rganlath3/DarkPassenger/Visual_Documentation/Base_MCU_TopView.png

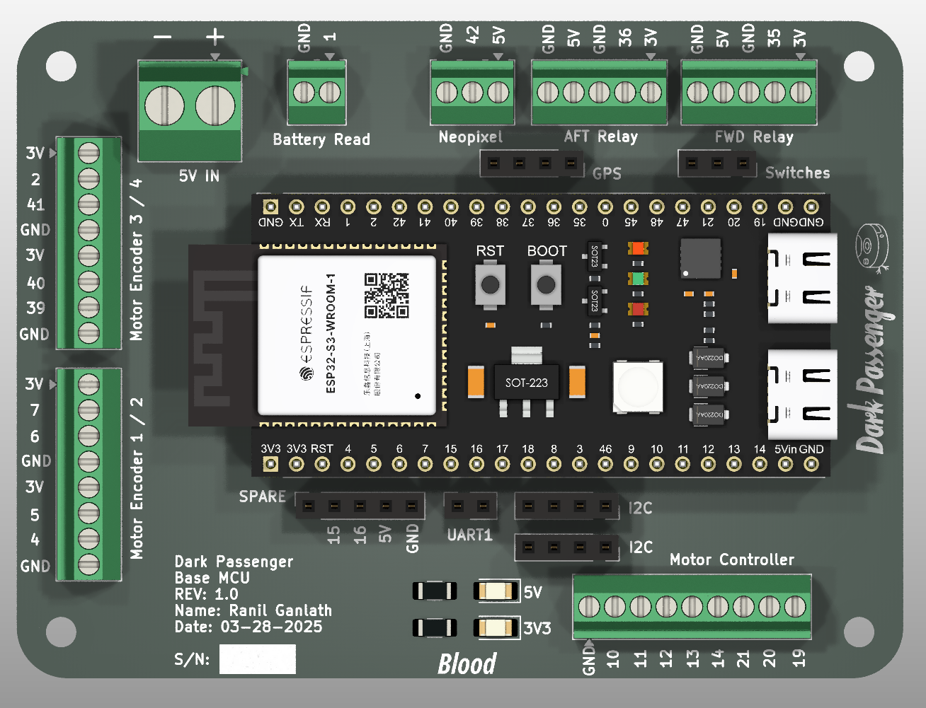
Visual_Documentation/Base_MCU_TopView.png
