rganlath3/DarkPassenger/Visual_Documentation/FrontView03192025.png

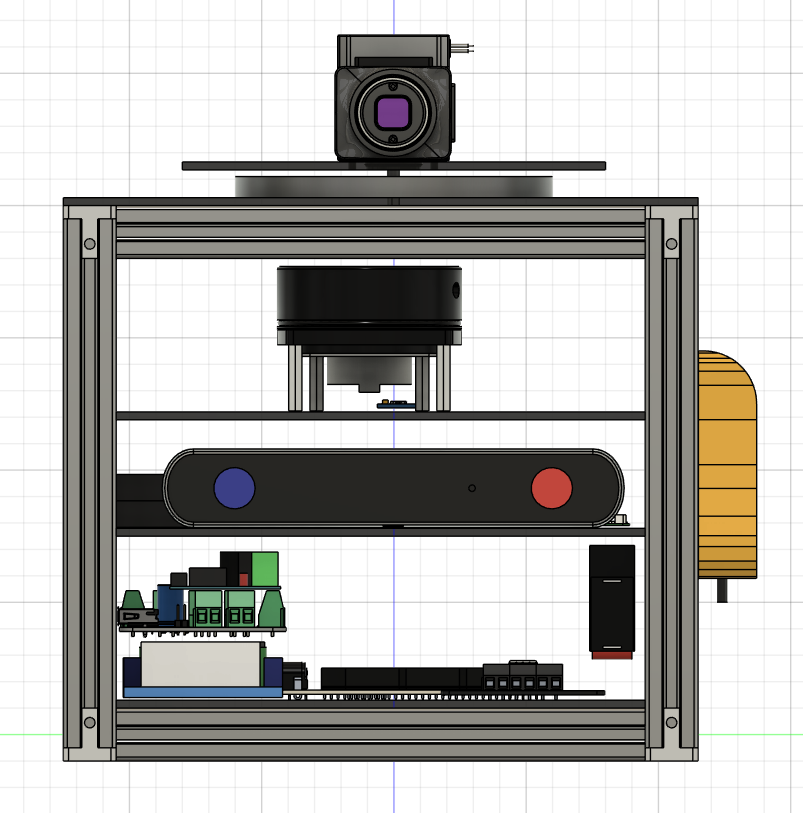
Visual_Documentation/FrontView03192025.png
