rganlath3/DarkPassenger/Visual_Documentation/PowerDistro_ISOUndersideView.png

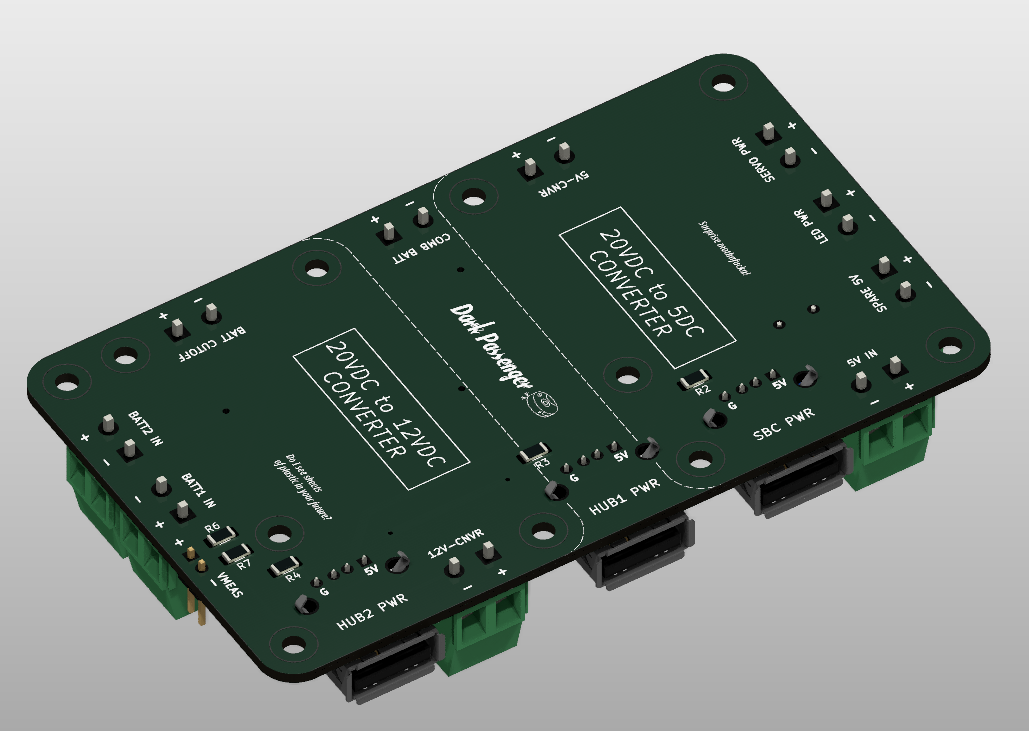
Visual_Documentation/PowerDistro_ISOUndersideView.png
