rganlath3/DarkPassenger/Visual_Documentation/SideView03192025.png

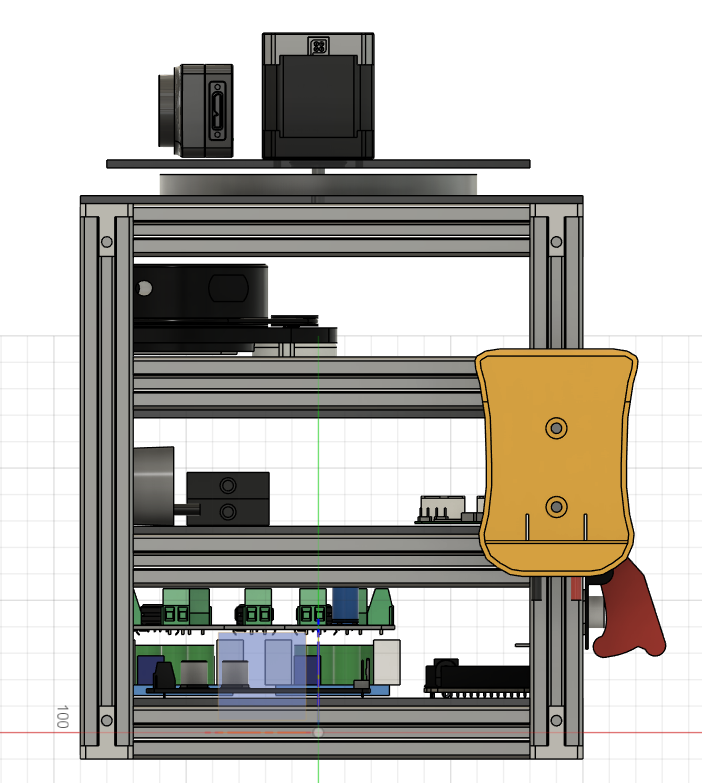
Visual_Documentation/SideView03192025.png
