rganlath3/DarkPassenger/Visual_Documentation/Turret_MCU_ISOUndersideView.png

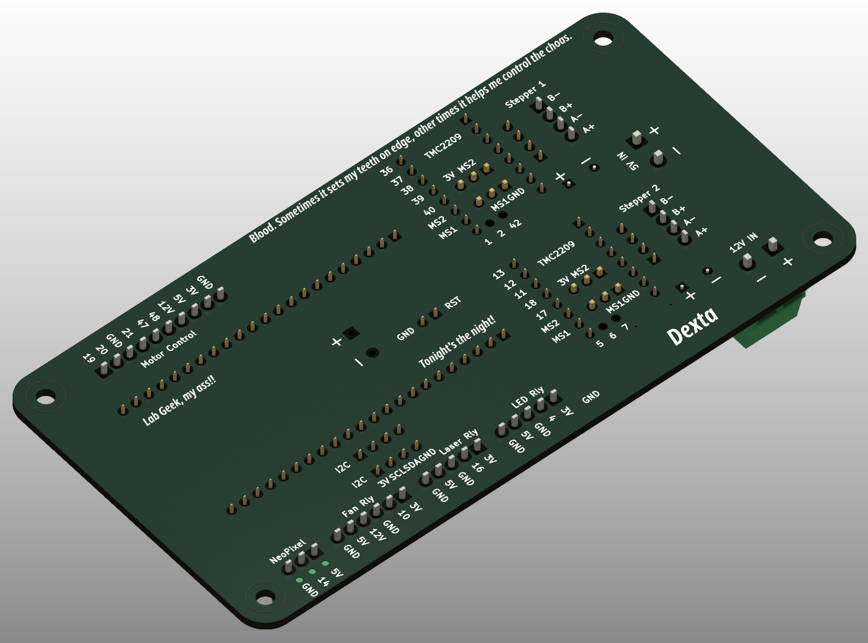
Visual_Documentation/Turret_MCU_ISOUndersideView.png
