rganlath3/DarkPassenger/Software_Development/MCU/Base_MCU/Testing_Scripts/2_IMS_MPU9250/2_IMS_MPU9250.ino

/*
  By Ranil Ganlath
  This is for testing an MPU9250. With the ESP32, any GPIO pin can be configured as SDA and SCL pins for I2C.
  Board: ESP32-S3-WROOM-1
  ESP32 8  - SDA
  ESP32 9  - SCL
  
  IDE Configuration:
  Arduino Board: ESP32S3 Dev Module
  Upload Speed: 921600
  USB Mode: Hardware CDC and JTAG
  USB CDC On Boot: Disabled
  USB Firmware MSC On Boot: Disabled
  USB DFU On Boot: Disabled
  Upload Mode: UART0/Hardware CDC
  CPU Freq: 240MHz
  Flash Mode: QIO 80MHz
  Flash Size: 4MB
  Parition Scheme: Default 4MB with spiffs
  Core Debug Level: None
  PSRAM: Disabled
  Arduino Runs On: Core 1
  Events Run On: Core 1
  Erash All Flash Before Sketch Upload: Disabled
  JTAG Adapter: Disabled
  Zigbee Mode: Disabled
*/

#include <MPU9250_asukiaaa.h>

#ifdef _ESP32_HAL_I2C_H_
#define SDA_PIN 8
#define SCL_PIN 9
#endif

MPU9250_asukiaaa mySensor;
float aX, aY, aZ, aSqrt, gX, gY, gZ, mDirection, mX, mY, mZ;

void setup() {
  Serial.begin(115200);
  while(!Serial);
  Serial.println("started");

#ifdef _ESP32_HAL_I2C_H_ // For ESP32
  Wire.begin(SDA_PIN, SCL_PIN);
  mySensor.setWire(&Wire);
#endif

  mySensor.beginAccel();
  mySensor.beginGyro();
  mySensor.beginMag();

  // You can set your own offset for mag values
  // mySensor.magXOffset = -50;
  // mySensor.magYOffset = -55;
  // mySensor.magZOffset = -10;
}

void loop() {
  uint8_t sensorId;
  int result;

  result = mySensor.readId(&sensorId);
  if (result == 0) {
    Serial.println("sensorId: " + String(sensorId));
  } else {
    Serial.println("Cannot read sensorId " + String(result));
  }

  result = mySensor.accelUpdate();
  if (result == 0) {
    aX = mySensor.accelX();
    aY = mySensor.accelY();
    aZ = mySensor.accelZ();
    aSqrt = mySensor.accelSqrt();
    Serial.println("accelX: " + String(aX));
    Serial.println("accelY: " + String(aY));
    Serial.println("accelZ: " + String(aZ));
    Serial.println("accelSqrt: " + String(aSqrt));
  } else {
    Serial.println("Cannod read accel values " + String(result));
  }

  result = mySensor.gyroUpdate();
  if (result == 0) {
    gX = mySensor.gyroX();
    gY = mySensor.gyroY();
    gZ = mySensor.gyroZ();
    Serial.println("gyroX: " + String(gX));
    Serial.println("gyroY: " + String(gY));
    Serial.println("gyroZ: " + String(gZ));
  } else {
    Serial.println("Cannot read gyro values " + String(result));
  }

  result = mySensor.magUpdate();
  if (result != 0) {
    Serial.println("cannot read mag so call begin again");
    mySensor.beginMag();
    result = mySensor.magUpdate();
  }
  if (result == 0) {
    mX = mySensor.magX();
    mY = mySensor.magY();
    mZ = mySensor.magZ();
    mDirection = mySensor.magHorizDirection();
    Serial.println("magX: " + String(mX));
    Serial.println("maxY: " + String(mY));
    Serial.println("magZ: " + String(mZ));
    Serial.println("horizontal direction: " + String(mDirection));
  } else {
    Serial.println("Cannot read mag values " + String(result));
  }

  Serial.println("at " + String(millis()) + "ms");
  Serial.println(""); // Add an empty line
  delay(500);
}
