rganlath3/DarkPassenger/Software_Development/MCU/Base_MCU/Testing_Scripts/6_GPS/6_GPS.ino

/*
  By Ranil Ganlath
  This is for testing a GY-NEO6MV2 GPS Module using an ESP32.
  Board: ESP32-S3-WROOM-1
  ESP32 38  - GPS TX2 Output (routes to RX)
  ESP32 37  - GPS RX2 Input (routes to TX)
  IDE Configuration:
  Arduino Board: ESP32S3 Dev Module
  Upload Speed: 921600
  USB Mode: Hardware CDC and JTAG
  USB CDC On Boot: Disabled
  USB Firmware MSC On Boot: Disabled
  USB DFU On Boot: Disabled
  Upload Mode: UART0/Hardware CDC
  CPU Freq: 240MHz
  Flash Mode: QIO 80MHz
  Flash Size: 4MB
  Parition Scheme: Default 4MB with spiffs
  Core Debug Level: None
  PSRAM: Disabled
  Arduino Runs On: Core 1
  Events Run On: Core 1
  Erash All Flash Before Sketch Upload: Disabled
  JTAG Adapter: Disabled
  Zigbee Mode: Disabled
*/

/*********
  Rui Santos & Sara Santos - Random Nerd Tutorials
  Complete instructions at https://RandomNerdTutorials.com/esp32-neo-6m-gps-module-arduino/
  Permission is hereby granted, free of charge, to any person obtaining a copy of this software and associated documentation files.
  The above copyright notice and this permission notice shall be included in all copies or substantial portions of the Software.
*********/

 // Define the RX and TX pins for Serial 2
#define RXD2 38
#define TXD2 37

#define GPS_BAUD 9600

// Create an instance of the HardwareSerial class for Serial 2
HardwareSerial gpsSerial(2);

void setup(){
  // Serial Monitor
  Serial.begin(115200);
  
  // Start Serial 2 with the defined RX and TX pins and a baud rate of 9600
  gpsSerial.begin(GPS_BAUD, SERIAL_8N1, RXD2, TXD2);
  Serial.println("Serial 2 started at 9600 baud rate");
}

void loop(){
  while (gpsSerial.available() > 0){
    // get the byte data from the GPS
    char gpsData = gpsSerial.read();
    Serial.print(gpsData);
  }
  delay(1000);
  Serial.println("-------------------------------");
}
