rganlath3/DarkPassenger/Software_Development/MCU/Base_MCU/WEB_SERVER_CONTROLLER/credentials_example.h

// credentials_example.h - Rename to credentials.h and update with your information
#ifndef CREDENTIALS_H
#define CREDENTIALS_H

const char* ssid = "wifi-network-name";
const char* password = "wifi-password";

#endif
